alexwarg/car-radio-acc-delay/src/img_delay.h

#pragma once

#include "cxx_pgm.h"

struct img_delay {
  static constexpr unsigned w = 32;
  static constexpr unsigned h = 16;
  static constexpr auto const data = Pgm((unsigned char const []){
   0xFE, 0x7F, 0xFE, 0x7F, 0x06, 0x60, 0x0E, 0x70, 0xFC, 0x3F, 0xF8, 0x1F, 0x00, 0x00, 0xFE, 0x7F, 
   0xFE, 0x7F, 0x86, 0x61, 0x86, 0x61, 0x06, 0x60, 0x00, 0x00, 0xFE, 0x7F, 0xFE, 0x7F, 0x00, 0x60, 
   0x00, 0x60, 0x00, 0x60, 0x00, 0x00, 0xFC, 0x7F, 0xFE, 0x7F, 0x06, 0x03, 0x06, 0x03, 0xFE, 0x7F, 
   0xFC, 0x7F, 0x00, 0x00, 0x7E, 0x00, 0xFE, 0x00, 0xC0, 0x7F, 0xC0, 0x7F, 0xFE, 0x00, 0x7E, 0x00
  });

};
