alexwarg/car-radio-acc-delay/src/img_off.h

#pragma once

#include "cxx_pgm.h"

struct img_off {
  static constexpr unsigned w = 19;
  static constexpr unsigned h = 16;
  static constexpr auto const data = Pgm((unsigned char const []){
   0xF8, 0x1F, 0xFC, 0x3F, 0x0E, 0x70, 0x06, 0x60, 0x0E, 0x70, 0xFC, 0x3F, 0xF8, 0x1F, 0x00, 0x00, 
   0xFE, 0x7F, 0xFE, 0x7F, 0x86, 0x01, 0x86, 0x01, 0x06, 0x00, 0x00, 0x00, 0xFE, 0x7F, 0xFE, 0x7F, 
   0x86, 0x01, 0x86, 0x01, 0x06, 0x00
  });

};
