alexwarg/car-radio-acc-delay/src/img_set.h

#pragma once

#include "cxx_pgm.h"

struct img_set {
  static constexpr unsigned w = 27;
  static constexpr unsigned h = 16;
  static constexpr auto const data = pgm_array<unsigned char>(
   0x00, 0xF8, 0xFC, 0x8C, 0x8C, 0x8C, 0x8C, 0x9C, 0x18, 0x00, 0xFC, 0xFC, 0x8C, 0x8C, 0x8C, 0x8C, 
   0x0C, 0x00, 0x0C, 0x0C, 0x0C, 0xFC, 0xFC, 0x0C, 0x0C, 0x0C, 0x00, 0x00, 0x18, 0x39, 0x31, 0x31, 
   0x31, 0x31, 0x3F, 0x1F, 0x00, 0x3F, 0x3F, 0x31, 0x31, 0x31, 0x31, 0x30, 0x00, 0x00, 0x00, 0x00, 
   0x3F, 0x3F, 0x00, 0x00, 0x00, 0x00
  );

};
