alexwarg/car-radio-acc-delay/src/img_settings.h

#pragma once

#include "cxx_pgm.h"

struct img_settings {
  static constexpr unsigned w = 16;
  static constexpr unsigned h = 16;
  static constexpr auto const data = Pgm((unsigned char const []){
   0x00, 0x00, 0x80, 0x01, 0x88, 0x11, 0xDC, 0x3B, 0xF8, 0x1F, 0x30, 0x0C, 0x18, 0x18, 0x9E, 0x79, 
   0x9E, 0x79, 0x18, 0x18, 0x30, 0x0C, 0xF8, 0x1F, 0xDC, 0x3B, 0x88, 0x11, 0x80, 0x01, 0x00, 0x00
  });

};
