alexwarg/car-radio-acc-delay/src/timer.h

// Licensed under the MIT License. See LICENSE.txt file in the project root.

#pragma once

#include "irq_guard.h"
#include "cxx_duration.h"

namespace cxx {

/**
 * Timer counter helper for AVR.
 *
 * Manages a counter on top of the AVR timer counter unit.
 * Hnadles the atomic access to the ounter as well as an intrnal representation for the
 * 40bit counter value...
 */

struct Timer
{
private:
  //uint8_t volatile &tcnt() const { return TCNT0; }
  uint8_t volatile &tcnt() const { return TCNT1; }

public:
  __uint24 _cnt = 0;

  using Cnt_type = cxx::qseconds_bits<24>;
  template<unsigned bits = 32>
  using Hires_type = cxx::duration<cxx::uint_for_bits_t<bits>, std::ratio<1, 1024>>;
  using Time_type = Hires_type<>;

  Cnt_type cnt() const
  {
    cxx::Irq_guard g;
    return _cnt;
  }

  Cnt_type cnt_locked() const
  {
    return _cnt;
  }


  template<bool locked = false>
  Hires_type<> now() const
  {
    union {
      uint32_t r;
      struct {
        uint8_t x;
        __uint24 t;
      };
    } n;

    uint8_t c = tcnt();
    if (!locked)
      {
        cxx::Irq_guard g;
        n.t = _cnt;
      }
    else
      n.t = _cnt;

    n.x = tcnt();
    if (n.x < c)
      n.r += (1 << 8);

    return Hires_type<>(n.r);
  }

  template<bool locked = false, typename T>
  std::enable_if_t<std::ratio_equal<typename T::period, Hires_type<>::period>::value>
  now(T &n) const
  {
    n = this->now<locked>();
  }

  template<bool locked = false, typename T>
  std::enable_if_t<std::ratio_equal<typename T::period, Cnt_type::period>::value>
  now(T &n) const
  {
    if (locked)
      n = cnt_locked();
    else
      n = cnt();
  }

};

}
